JOJOCAFE/RV8/RV8GR/doc/labs/lab02_ring_counter.md

# Lab 02: Ring Counter — สร้างจังหวะ T0/T1/T2

**เป้าหมาย**: ต่อ U8 (74HC164) + U24 (74HC04) ให้สร้างจังหวะ 3 เฟส

---

## อุปกรณ์

| ชิ้น | ชื่อ | จำนวน |
|:----:|---|:-----:|
| 1 | 74HC164 (U8) | 1 |
| 2 | 74HC04 (U24) | 1 |
| 3 | LED สีเขียว 3mm | 3 |
| 4 | 330Ω resistor | 3 |
| 5 | 100nF capacitor | 2 |
| 6 | Push button (Reset) | 1 |
| 7 | 10kΩ resistor | 1 |

---

## วงจร

### Pinout: 74HC164 (U8)

```
        ┌───U───┐
   A  1 │       │ 14 VCC
   B  2 │       │ 13 Q7
  Q0  3 │ 164   │ 12 Q6
  Q1  4 │       │ 11 Q5
  Q2  5 │       │ 10 Q4
  Q3  6 │       │  9 /CLR
 GND  7 │       │  8 CLK
        └───────┘
```

### Pinout: 74HC04 (U24) — ใช้แค่ 2 gate

```
        ┌───U───┐
  1A  1 │       │ 14 VCC
  1Y  2 │       │ 13
  2A  3 │ 04    │ 12
  2Y  4 │       │ 11
     ...│       │...
 GND  7 │       │  8
        └───────┘
```

### การต่อสาย

```
1. ไฟเลี้ยง:
   U8 pin 14 (VCC) → 5V        U8 pin 7 (GND) → GND
   U24 pin 14 (VCC) → 5V       U24 pin 7 (GND) → GND
   100nF คร่อม VCC-GND ทั้ง 2 ตัว

2. Ring counter feedback:
   U8 pin 3 (Q0) → U24 pin 1 (1A)     [Q0 เข้า inverter 1]
   U24 pin 2 (1Y) → U8 pin 1 (A)      [NOT Q0 → A]
   
   U8 pin 4 (Q1) → U24 pin 3 (2A)     [Q1 เข้า inverter 2]
   U24 pin 4 (2Y) → U8 pin 2 (B)      [NOT Q1 → B]

3. Clock:
   U8 pin 8 (CLK) → สาย CLK จาก Lab 01 (ปุ่มกด)

4. Reset:
   U8 pin 9 (/CLR) → ปุ่ม Reset (ปกติ HIGH, กด = LOW)
   [ต่อ: 5V → 10kΩ → pin 9 ← ปุ่ม → GND]

5. LED ดู output:
   U8 pin 3 (Q0=T0) → 330Ω → LED → GND
   U8 pin 4 (Q1=T1) → 330Ω → LED → GND
   U8 pin 5 (Q2=T2) → 330Ω → LED → GND
```

---

## ทำไมวงจรนี้ถึงวนครบ 3?

74HC164: serial input = **A AND B** (ต้อง HIGH ทั้งคู่ถึงจะ shift 1 เข้า)

| สถานะ | Q2 Q1 Q0 | A=NOT(Q0) | B=NOT(Q1) | A AND B | ถัดไป |
|:---:|:---:|:---:|:---:|:---:|:-----:|
| Reset | 0 0 0 | 1 | 1 | **1** | 0 0 1 |
| T0 | 0 0 1 | 0 | 1 | **0** | 0 1 0 |
| T1 | 0 1 0 | 1 | 0 | **0** | 1 0 0 |
| T2 | 1 0 0 | 1 | 1 | **1** | 0 0 1 ← วนกลับ T0! |

วงจรนี้คือ **3-state FSM** — มี 3 สถานะ วนซ้ำ ตลอดไป

### Timing Diagram

```
CLK  ─┐ ┌─┐ ┌─┐ ┌─┐ ┌─┐ ┌─┐ ┌─┐ ┌─
      └─┘ └─┘ └─┘ └─┘ └─┘ └─┘ └─┘

T0   ───██████─────────────██████────
T1   ─────────██████─────────────████
T2   ─────────────────██████─────────

     │← 1 คำสั่ง →│← 1 คำสั่ง →│
```

### จังหวะนี้ใช้ทำอะไรใน CPU?

ทุกคำสั่งของ RV8-GR ใช้ 3 clock = 3 จังหวะ:

```
ตัวอย่าง: LI $42 (โหลดค่า $42 เข้า accumulator)

T0: อ่าน opcode $10 จาก ROM    → บอก CPU ว่า "LI"
T1: อ่าน operand $42 จาก ROM   → ค่าที่ต้องโหลด
T2: execute → AC ← $42          → ทำงานจริง!
```

LED 3 ดวงที่เห็นใน lab นี้ = สัญญาณจริงที่ไปควบคุม U5 (IR), U6 (IRL), U9 (AC), PC ทั้งหมดใน lab ถัดๆ ไป

> ⚠️ **เรื่อง Clock Bounce**
>
> Ring Counter เป็นจุดแรกที่ bounce สร้างปัญหาจริง
> ถ้ากดปุ่ม 1 ครั้งแล้ว LED กระโดดข้ามสถานะ (เช่น T0→T2 ข้าม T1)
> แสดงว่า bounce ทำให้เกิดหลาย clock edge
>
> วิธีแก้: กดปุ่มช้าๆ ค้างไว้สักครู่แล้วค่อยปล่อย
> ถ้ายังมีปัญหา → เพิ่ม capacitor 100nF ที่ปุ่มกด
> (lab ถัดไปจะเพิ่ม 74HC14 Schmitt Trigger ให้ clean ขึ้น)

---

## ทดสอบ ✅

### ขั้นตอน

1. เสียบไฟ → LED ทั้ง 3 อาจติดหรือดับ (ยังไม่ reset)
2. **กด Reset** → LED ทั้ง 3 ดับ (Q0=Q1=Q2=0)
3. **กด Clock ครั้งที่ 1** → T0 ติด, T1 ดับ, T2 ดับ
4. **กด Clock ครั้งที่ 2** → T0 ดับ, T1 ติด, T2 ดับ
5. **กด Clock ครั้งที่ 3** → T0 ดับ, T1 ดับ, T2 ติด
6. **กด Clock ครั้งที่ 4** → T0 ติด! (วนกลับมา!)

### ตาราง LED

| กด Clock | T0 (Q0) | T1 (Q1) | T2 (Q2) | ถูก? |
|:---:|:---:|:---:|:---:|:----:|
| Reset | ○ | ○ | ○ | ☐ |
| 1 | ● | ○ | ○ | ☐ |
| 2 | ○ | ● | ○ | ☐ |
| 3 | ○ | ○ | ● | ☐ |
| 4 | ● | ○ | ○ | ☐ |
| 5 | ○ | ● | ○ | ☐ |
| 6 | ○ | ○ | ● | ☐ |

● = LED ติด, ○ = LED ดับ

### ทดสอบความทนทาน

| # | ทดสอบ | ผลที่ต้องได้ | ผ่าน? |
|:-:|---|---|:-----:|
| 6 | ต่อ 555 timer (1Hz) ปล่อย 1000+ cycles | T0→T1→T2 ไม่เคยหลุด | ☐ |

> 📌 **Illegal State Recovery**: หาก power-up ได้สถานะผิด
> วงจรจะเข้าสู่ลูป T0→T1→T2 ได้เองภายในไม่กี่ clock cycles
> (feedback A AND B = NOT(Q0) AND NOT(Q1) ทำหน้าที่ self-correct)
> ถ้ารอ 5-6 clocks แล้วยังไม่วนปกติ → กด Reset ให้ Q0-Q2=000
> แล้วปล่อย clock 1 ครั้งเพื่อเข้า T0

### State Machine (ภาพรวมหัวใจ CPU)

```
        ┌────────────────────────────┐
        │                            │
        ▼                            │
    ┌───────┐     ┌───────┐     ┌───────┐
    │  T0   │────→│  T1   │────→│  T2   │
    │ (001) │     │ (010) │     │ (100) │
    │ Fetch │     │Operand│     │Execute│
    └───────┘     └───────┘     └───────┘
```

> ทุกคำสั่งใน RV8-GR วนรอบนี้ตลอด — ไม่มี stall, ไม่มี wait state

### Optional: Debug Header (Q3-Q7)

ถ้าอยากตรวจ illegal state ได้ชัดขึ้น:

```
U8 pin 6  (Q3) → test point (หรือ LED)
U8 pin 10 (Q4) → test point
U8 pin 11 (Q5) → test point
U8 pin 12 (Q6) → test point
U8 pin 13 (Q7) → test point
```

> ปกติ Q3-Q7 ต้องเป็น 0 ตลอด
> ถ้าเห็น Q3+ ติด = ring counter หลุด state → กด Reset

---

## ถ้าไม่ถูก?

| อาการ | สาเหตุ | แก้ |
|---|---|-----|
| LED ไม่ติดเลย | ไฟไม่ถึง IC | เช็ค VCC/GND |
| T0 ค้างติดตลอด | inverter ต่อผิด | เช็ค U24 pin 1→2, pin 3→4 |
| วนไม่ครบ 3 | A,B ต่อสลับ | สลับ U8 pin 1 กับ pin 2 |
| กด Reset แล้วไม่ clear | /CLR ไม่ถึง LOW | เช็คปุ่ม Reset |

---

## ซอฟต์แวร์จำลอง

รัน sim_lab เปรียบเทียบ:
```bash
cd RV8GR/sim/sim_lab
python3 lab02_ring_counter.py
```

---

## สิ่งที่ได้

- ✅ จังหวะ T0→T1→T2 วนได้ถูกต้อง
- ✅ CPU ต้องการจังหวะนี้เพื่อทำงาน 3 ขั้นตอน/คำสั่ง
- ✅ T0 = อ่านคำสั่ง, T1 = อ่าน operand, T2 = ทำงาน

### สิ่งที่พิสูจน์ได้แล้ว

```
✓ มี clock (Lab 01)
✓ มี reset (Lab 01)
✓ มี state machine (Lab 02) ← อยู่ตรงนี้!
✓ มี one-hot encoding
✓ มี fetch/execute timing
```

> 📌 CPU ที่เหลือทั้งหมด (U1-U34) จะใช้ T0/T1/T2 นี้เป็นจังหวะกลางร่วมกัน
> LED 3 ดวงนี้ = สัญญาณจริงที่ควบคุม CPU ทั้งตัว!

**ผ่านทุกข้อ → ไป Lab 03!** 🎉
