JOJOCAFE/RV8/JOJOCAFE-Org/.agent_state/sw-coder/MEMORY.md

# SW Coder Memory

## Tools Built

| Tool | Status | Purpose |
|---|---|---|
| `tools/rv8gr_asm.py` | ✅ done | Assembler (18 opcodes + macros) |
| `sim/chip_sim.py` | ✅ done | Gate-level sim (34 logic chips + ROM/RAM) |
| `sim/soft_debug.py` | ✅ done | High-level trace sim |
| `rv8flash.py` | ✅ done | ROM programmer (flash/read/verify) |
| `rv8term.py` | ✅ done | Terminal bridge via /SLOT1 |

## Assembler Features

- 18 opcodes + macros (CLR, INC, DEC, NOT, NOTI)
- Cross-page validation
- Overlap detection
- .memh output for Verilog
- Page-safe branch checking

## ISA Quick Ref

- Immediate: opcode, imm (2 bytes, SRC=0)
- Register: opcode, rs/rd (2 bytes, SRC=1 or STR=1)
- Branch/Jump: opcode, addr_lo (2 bytes, uses Page Register)

## Programmer Protocol

- `?` → `Connected\n` (identify)
- `F` + 32KB → `D\n` (flash)
- `V` → 32KB (verify/read)
- `R` → `K\n` (run mode)

## Pending

- Example programs (.asm): blink, counter, game, BASIC stub
- RV8-R assembler (when ISA designed)
- Components backend now has schematic/netlist/probe/test-logic foundations. Next work should keep JSON/block/Python APIs round-trippable and frontend-agnostic.

## Components Python Simulator

- Shared path: `/home/jo/kiro/Components/python`
- `chiplib.loader` loads `.bin`, Intel HEX, or text-hex into ROM/RAM `.data` before simulation.
- `StimulusController` default is 64 input channels (`IN0..IN63`) and 8 clock channels (`CLK0..CLK7`).
- Keep the backend frontend-agnostic for future JS/web service wrappers or Python-native UI.
- Clock stimulus is edge-aware and should drive physical pins, not abstract CPU clocks.
