JOJOCAFE/RV8/RV8GR/doc/labs/lab03_pc_counter.md

# Lab 03: Program Counter — นับตำแหน่งคำสั่ง

**เป้าหมาย**: ต่อ U1-U4 (74HC161 ×4) เป็น counter 16 บิต นับขึ้นทีละ 1

---

## อุปกรณ์

| ชิ้น | ชื่อ | จำนวน |
|:----:|---|:-----:|
| 1 | 74HC161 (U1-U4) | 4 |
| 2 | LED สีเขียว 3mm | 8 |
| 3 | 330Ω resistor | 8 |
| 4 | 100nF capacitor | 4 |

---

## วงจร

### Pinout: 74HC161

```
          ┌───U───┐
  /CLR  1 │       │ 16 VCC
   CLK  2 │       │ 15 RCO
    D0  3 │ 161   │ 14 QA (bit 0)
    D1  4 │       │ 13 QB (bit 1)
    D2  5 │       │ 12 QC (bit 2)
    D3  6 │       │ 11 QD (bit 3)
   ENP  7 │       │ 10 ENT
   GND  8 │       │  9 /LD
          └───────┘
```

### การต่อสาย

```
ทุกตัว (U1-U4):
  pin 16 (VCC) → 5V
  pin 8 (GND) → GND
  pin 1 (/CLR) → ปุ่ม Reset (ปกติ HIGH)
  pin 2 (CLK) → สาย CLK จาก Lab 01
  pin 7 (ENP) → 5V (enable นับตลอด)
  pin 9 (/LD) → 5V (ไม่ load, นับอย่างเดียว)
  100nF คร่อม VCC-GND ทุกตัว

Cascade (ต่อพ่วง):
  U1 pin 10 (ENT) → 5V (ตัวแรก enable ตลอด)
  U1 pin 15 (RCO) → U2 pin 10 (ENT)
  U2 pin 15 (RCO) → U3 pin 10 (ENT)
  U3 pin 15 (RCO) → U4 pin 10 (ENT)

LED (ดู 8 บิตล่าง = U1 + U2):
  U1 pin 14 (QA=bit0) → 330Ω → LED → GND
  U1 pin 13 (QB=bit1) → 330Ω → LED → GND
  U1 pin 12 (QC=bit2) → 330Ω → LED → GND
  U1 pin 11 (QD=bit3) → 330Ω → LED → GND
  U2 pin 14 (QA=bit4) → 330Ω → LED → GND
  U2 pin 13 (QB=bit5) → 330Ω → LED → GND
  U2 pin 12 (QC=bit6) → 330Ω → LED → GND
  U2 pin 11 (QD=bit7) → 330Ω → LED → GND
```

---

## ทดสอบ ✅

### ขั้นตอน

1. กด Reset → LED ทั้ง 8 ดับ (PC = 0000 0000)
2. กด Clock ทีละครั้ง → LED นับขึ้น:

### ตาราง LED (อ่านจากขวาไปซ้าย = bit7...bit0)

| กด | bit7 | bit6 | bit5 | bit4 | bit3 | bit2 | bit1 | bit0 | ค่า | ถูก? |
|:--:|:----:|:----:|:----:|:----:|:----:|:----:|:----:|:----:|:---:|:----:|
| Reset | ○ | ○ | ○ | ○ | ○ | ○ | ○ | ○ | $00 | ☐ |
| 1 | ○ | ○ | ○ | ○ | ○ | ○ | ○ | ● | $01 | ☐ |
| 2 | ○ | ○ | ○ | ○ | ○ | ○ | ● | ○ | $02 | ☐ |
| 3 | ○ | ○ | ○ | ○ | ○ | ○ | ● | ● | $03 | ☐ |
| 4 | ○ | ○ | ○ | ○ | ○ | ● | ○ | ○ | $04 | ☐ |
| 15 | ○ | ○ | ○ | ○ | ● | ● | ● | ● | $0F | ☐ |
| 16 | ○ | ○ | ○ | ● | ○ | ○ | ○ | ○ | $10 | ☐ |

● = LED ติด (1), ○ = LED ดับ (0)

**สำคัญ**: ถ้ากด 16 ครั้งแล้ว bit4 ติด = cascade ทำงาน!

> 📝 **หมายเหตุ: PC จริงใน RV8-GR**
>
> Lab นี้ต่อ ENP=ENT=VCC ทำให้ PC นับ **ทุก clock** เพื่อความง่าย
>
> แต่ใน CPU จริง PC จะนับเฉพาะ T0 และ T1 (ไม่นับใน T2)
> ผ่านสัญญาณ `PC_INC = T0 OR T1` จาก Ring Counter (Lab 02)
>
> ```
> U4  U3  U2  U1
> [15:12] [11:8] [7:4] [3:0]  ← PC 16 บิตเต็ม
> ```
>
> LED 8 ดวงที่เห็นใน lab นี้ = PC[7:0] เท่านั้น (PC[15:8] ยังมีอยู่ใน U3-U4)

---

## ถ้าไม่ถูก?

| อาการ | สาเหตุ | แก้ |
|---|---|-----|
| ไม่นับเลย | ENP หรือ ENT ไม่ HIGH | เช็คสาย pin 7, 10 |
| นับแค่ 0-15 วน | U2 ENT ไม่ต่อ U1 RCO | ต่อ U1-15 → U2-10 |
| นับ 2 ทีละครั้ง | Clock bounce | เพิ่ม 100nF ที่ปุ่ม |
| Reset ไม่ทำงาน | /CLR ค้าง HIGH | เช็คปุ่ม Reset |

---

## ซอฟต์แวร์จำลอง

```bash
cd RV8GR/sim/sim_lab
python3 lab03_pc_counter.py
```

---

## Challenge (ไม่บังคับ — สำหรับคนที่อยากลองเพิ่ม)

### Challenge A: PC_INC — ให้ Ring Counter ควบคุม PC

```
ถอด ENP/ENT จาก VCC
ต่อ ENP (U1-7) ← T0 (U8-3) [หรือ T0 OR T1]
ต่อ ENT (U1-10) ← T0 (U8-3)
```

สังเกต: PC จะนับเฉพาะเมื่อ T0=HIGH → **Control Unit ควบคุม PC!**

### Challenge B: Parallel Load — ทำ Jump

```
ต่อ DIP switch 4 บิต → U1 pin 3,4,5,6 (D0-D3)
ดึง /LD (pin 9) ลง LOW (ปุ่มกด)
กด Clock → PC โหลดค่าจาก switch!
```

นี่คือวิธีที่คำสั่ง J (Jump) ทำงานใน CPU จริง:
/PC_LD = LOW → PC ← target address

---

## สิ่งที่ได้

- ✅ Counter 16 บิต นับ $0000 → $FFFF
- ✅ Reset กลับ $0000 ได้
- ✅ Cascade: U1 เต็ม → U2 นับต่อ → U3 → U4
- ✅ นี่คือ Program Counter ของ CPU!

**ผ่านทุกข้อ → ไป Lab 04!** 🎉
