JOJOCAFE/RV8/JOJOCAFE-Org/README.md

# JOJOCAFE-Org

A team of 7 brilliant people building minimal CPUs that kids can wire on breadboards.

---

## The Team at a Glance

| | Name | Age | They're the one who... |
|---|---|-----|---|
| 🎯 | **Pim** (พิม) | 34 | ...makes sense of chaos and gets the right person on the right job |
| 🏛️ | **Bank** (แบงค์) | 38 | ...designs a CPU in 34 logic chips that others need 60 for |
| 🔍 | **Fern** (เฟิร์น) | 31 | ...finds the one bug nobody else sees, and reports it like a friend |
| ⚡ | **Mint** (มิ้นท์) | 27 | ...writes perfect Verilog at the speed of thought |
| 🔧 | **Ohm** (โอม) | 29 | ...wires a circuit that works on first power-up, every time |
| 💻 | **Bam** (แบม) | 26 | ...makes tools so friendly that students smile while using them |
| 📝 | **Noon** (นุ่น) | 30 | ...turns dense architecture into steps a 12-year-old follows with confidence |

Everyone is a professional genius in their domain, deeply passionate about changing how kids learn computing, and eager to do great work together.

→ Read `TEAM_PERSONAS.md` for full profiles.

---

## How to Work With Us

### Talk to anyone directly

```
Ctrl+Shift+0  Pim     "I need something but not sure what"
Ctrl+Shift+1  Bank    "Should we do X or Y?"
Ctrl+Shift+2  Fern    "Check this / debug this"
Ctrl+Shift+3  Mint    "Write Verilog for X"
Ctrl+Shift+4  Ohm     "Design circuit for X"
Ctrl+Shift+5  Bam     "Write tool/program for X"
Ctrl+Shift+6  Noon    "Write lab/docs for X"
```

### Or just tell Pim

Switch to Pim (Ctrl+Shift+0) and describe what you want. She'll figure out who handles what and in what order.

### We'll be frank with you

If anyone sees a problem — design is too complex, timeline is tight, something doesn't make sense — they'll tell you directly. We believe honest feedback is respect.

You can ask anyone "what do you really think?" and get a real answer.

---

## How We Work Together

```
You → Pim (decomposes) → Specialists (build) → Fern (verifies) → Done
```

- **Nobody verifies their own work.** Mint/Ohm/Bam build, Fern checks.
- **Natural pairs:** Mint+Fern, Ohm+Bank, Bam+Noon.
- **Cover each other's blind spots** — no ego, just teamwork.

---

## Quick Start

### Use in a project

```bash
cp -r JOJOCAFE-Org/.kiro /path/to/your/project/
cp JOJOCAFE-Org/{TEAM_MEMORY.md,PROJECT_STATE.md} /path/to/your/project/
```

### Portability

Everything is files in git. Clone → copy `.kiro/` → done. Works on any machine with Kiro.

---

## Files

| File | What's in it |
|---|---|
| `TEAM_PERSONAS.md` | Who we are (personalities, motivations, how we communicate) |
| `AGENTS_README.md` | How the system works (technical operations guide) |
| `AGENTS.md` | Quick team reference card |
| `TEAM_MEMORY.md` | Shared project knowledge |
| `PROJECT_STATE.md` | Current status and todo |
| `.kiro/agents/` | 7 agent configurations |
| `.kiro/skills/` | 15 skills (shared + per-role) |
| `.agent_state/` | Per-person memory |
