JOJOCAFE/RV8/RV8GR/doc/05_understand_by_module.md

# RV8-GR — เข้าใจ CPU ทีละโมดูล (สำหรับน้อง ม.ต้น)

**สอน CPU 34 logic chips + ROM + RAM ตัวนี้ทีละขั้น ใช้ภาษาง่ายๆ ไม่รีบ อ่านจบแล้วต่อวงจรได้เลย**

---

## สารบัญ

1. CPU คืออะไร — ภาพรวม
2. จังหวะนาฬิกา T0/T1/T2 (U8)
3. Program Counter — ตัวชี้คำสั่ง (U1-U4)
4. Instruction Register — ตัวจำคำสั่ง (U5, U6)
5. DBUS, IBUS — ถนนข้อมูล (U7, U14)
6. ALU — เครื่องคำนวณ (U10-U13, U19-U20)
7. AC Mux — เลือกผลลัพธ์ (U17-U18)
8. Address Mux — เลือกที่อยู่ (U15-U16, U29-U30)
9. Z Flag — ธงศูนย์ (U21, U22)
10. Page Register — กระโดดไกล (U23)
11. Control Logic — สมองสั่งการ (U24-U28)
12. IRQ — ขัดจังหวะ (U31)
13. ROM กับ RAM — หน่วยความจำ
14. RV8-Bus — ถนนสู่โลกภายนอก (40-pin)
15. สรุป: ข้อมูลไหลอย่างไร
16. คำสั่งทั้งหมดของ RV8-GR (ISA)
17. CPU ทำงานจริง — ไล่ทีละ Clock
18. อ่านจบแล้ว ทำอะไรต่อ?

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

---

## 1. CPU คืออะไร — ภาพรวม

CPU เหมือนสมองของคอมพิวเตอร์ มันทำ 3 สิ่ง ซ้ำไปเรื่อยๆ:

### ภาพรวมทั้ง CPU (จำภาพนี้ไว้ตลอดทั้งเล่ม!)

```
                    ┌─────────┐
        ┌──────────│   ROM   │ ← เก็บโปรแกรม
        │          └─────────┘
        │               ↕ DBUS (ถนนภายนอก)
        │          ┌─────────┐
        │          │   U7    │ ← สะพานเชื่อม
        │          └─────────┘
        │               ↕ IBUS (ถนนภายใน)
        │    ┌──────────┼──────────┐
        │    │          │          │
   ┌────┴──┐│    ┌─────┴────┐   ┌─┴───┐
   │  PC   ││    │   ALU    │   │ AC  │ ← ผลลัพธ์
   │(U1-U4)││    │(U10-U13) │   │(U9) │
   └───────┘│    └──────────┘   └─────┘
        ↑   │          ↑              │
        │   │    ┌─────┴────┐         │
   กระโดด  │    │  IR (U5) │ ← คำสั่ง │
        │   │    └──────────┘         ↓
        │   │                    ┌─────────┐
        │   └───────────────────→│   RAM   │ ← เก็บข้อมูล
        │                        └─────────┘
   Page Reg (U23)
```

### Fetch → Fetch → Execute (หัวใจของ CPU!)

CPU ตัวนี้ไม่มี "Decode" แยก เพราะ opcode = สัญญาณควบคุมโดยตรง!

ทุกคำสั่งใช้ 3 จังหวะ ลองดูตัวอย่าง `ADDI $05` (บวก 5):

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

```
T0: PC ชี้ ROM → ได้ "$10" → IR จำไว้ (="บวก")
T1: PC ชี้ ROM → ได้ "$05" → IR จำไว้ (="5")
T2: ALU ทำ AC + 5 → AC = ผลลัพธ์ใหม่!
```

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

```
1. อ่านคำสั่ง (จาก ROM)
2. เข้าใจคำสั่ง (แปลเป็นสัญญาณ)
3. ทำตามคำสั่ง (คำนวณ, เก็บค่า, กระโดด)
```

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

ทั้งหมดนี้ทำได้ด้วย 34 logic chips ไม่มี microcode ไม่มี lookup table.

---

## 2. จังหวะนาฬิกา T0/T1/T2 (U8)

**ทำไมต้องมีจังหวะ?**

ลองนึกภาพการทำขนมปัง:
1. หยิบแป้ง (T0)
2. ใส่ไส้ (T1)
3. ปิ้ง (T2)

CPU ก็เหมือนกัน — ทำทีละขั้น ขั้นละ 1 จังหวะนาฬิกา.

**ชิป U8 (74HC164)** สร้างจังหวะ:

```
CLK:  ⎽⎽⎽⎽╱‾‾‾‾╲⎽⎽⎽⎽╱‾‾‾‾╲⎽⎽⎽⎽╱‾‾‾‾╲⎽⎽⎽⎽╱‾‾‾‾╲⎽⎽⎽

T0:   ‾‾‾‾‾‾‾‾‾‾╲⎽⎽⎽⎽⎽⎽⎽⎽⎽⎽⎽⎽⎽⎽⎽⎽⎽⎽⎽⎽⎽⎽⎽╱‾‾‾‾‾‾‾‾‾‾
T1:   ⎽⎽⎽⎽⎽⎽⎽⎽⎽⎽╱‾‾‾‾‾‾‾‾‾‾╲⎽⎽⎽⎽⎽⎽⎽⎽⎽⎽⎽⎽⎽⎽⎽⎽⎽⎽⎽⎽⎽⎽⎽
T2:   ⎽⎽⎽⎽⎽⎽⎽⎽⎽⎽⎽⎽⎽⎽⎽⎽⎽⎽⎽⎽⎽╱‾‾‾‾‾‾‾‾‾‾╲⎽⎽⎽⎽⎽⎽⎽⎽⎽⎽⎽
        T0          T1          T2          T0 ...
```

มีบิตเดียวที่เป็น 1 วิ่งไป: Q0→Q1→Q2→Q0...

```
State Diagram (หัวใจ CPU):

    RESET → [T0] → [T1] → [T2] ─┐
              ↑                    │
              └────────────────────┘

ภายใน Shift Register:

    [1][0][0]  ← T0 active
         ↓ clock
    [0][1][0]  ← T1 active
         ↓ clock
    [0][0][1]  ← T2 active
         ↓ clock (feedback วนกลับ)
    [1][0][0]  ← T0 อีกรอบ!
```

> 📌 มีบิต "1" เพียงตัวเดียววิ่งวนในวงแหวน — เรียกว่า **one-hot encoding**
> ถ้ารีเซ็ต จะกลับมาเป็น T0 เสมอ

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

---

## 3. Program Counter — ตัวชี้คำสั่ง (U1-U4)

**ทำไมต้องมี PC?**

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

**ชิป**: U1-U4 (74HC161 × 4 ตัว = 16 บิต)

```
ทำงาน 3 แบบ:
1. นับขึ้น +1  (ตอน T0, T1 → อ่านคำสั่งถัดไป)
2. หยุดนับ     (ตอน T2 → ทำงาน ไม่ต้องอ่านเพิ่ม)
3. กระโดด     (ตอน jump → ใส่ค่าใหม่เข้า PC)
```

**ตัวอย่าง**:
```
PC = $0000 → อ่าน ROM ที่ $0000 (คำสั่ง LI $10)
PC = $0001 → อ่าน ROM ที่ $0001 (operand $10)
PC = $0002 → อ่าน ROM ที่ $0002 (คำสั่งถัดไป)
...
PC = $0020 ← J $20 สั่ง jump → PC กระโดดไปตรงนี้!
```

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

---

## 4. Instruction Register — ตัวจำคำสั่ง (U5, U6)

**ทำไมต้องจำคำสั่ง?**

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

ต้องจำไว้เพื่อใช้ตอน T2 (execute).

**U5 (IR_HIGH)** — จำ control byte:
```
ตัวอย่าง: ADDI → control byte = $10 = 00010000
                                        │││││││└─ JMP=0
                                        ││││││└── BR=0
                                        │││││└─── STR=0
                                        ││││└──── SRC=0
                                        │││└───── AC_WR=1 ← เขียน AC!
                                        ││└────── MUX_SEL=0
                                        │└─────── XOR_MODE=0
                                        └──────── ALU_SUB=0
```

**U6 (IR_LOW)** — จำ operand:
```
ตัวอย่าง: ADDI $05 → operand = $05 = ค่าที่จะบวก
```

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

---

## 5. DBUS, IBUS — ถนนข้อมูล (U7, U14)

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

**2 ถนนข้อมูล:**

```
┌─────────────────────────────────────────────────┐
│  โลกภายนอก (ROM, RAM)                            │
│          ↕ DBUS (D0-D7)                          │
│      ┌───────┐                                   │
│      │  U7   │  ← Bus Buffer (สะพาน)             │
│      └───────┘                                   │
│          ↕ IBUS (IBUS0-IBUS7)                        │
│  โลกภายใน (ALU, registers)                       │
└─────────────────────────────────────────────────┘
```

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

**กฎสำคัญ: ทางเดินเดียว!**

IBUS มี 3 คนที่ส่งข้อมูลได้ แต่ **ทีละคนเท่านั้น**:

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

```
U7 /OE = BUF_OE_N
WR_DIR = NOT(/AC_BUF)
ROM /OE = WR_DIR
→ ถ้า STR=1 (STORE active): U14 ขับ IBUS, U7 ส่ง IBUS→DBUS, ROM ปิด output
```

---

## 6. ALU — เครื่องคำนวณ (U10-U13, U19-U20)

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

**เคล็ดลับ: ใช้ XOR gate ทำทั้ง 3 อย่าง!**

```
                    IBUS (ค่าที่จะคำนวณ)
                      │
              ┌───────┴───────┐
              │   U12-U13     │  ← XOR gates
              │   A=IBUS      │
              │   B=??? ←─────┼── U19-U20 (mux เลือก)
              └───────┬───────┘
                      │
              XOR output
                ╱          ╲
    ┌──────────┘            └──────────┐
    │ U10-U11 (Adder)                  │ U17-U18 (AC mux B)
    │ A = AC                           │ → ส่งตรงเข้า AC
    │ B = XOR output                   │   (สำหรับ LI, XOR)
    │ Cin = SUB bit                    │
    │ SUM = ผลบวก                      │
    └──────────────────────────────────┘
```

**3 โหมด:**

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

**ทำไมลบได้?**
```
ลบ = บวกกับจำนวนลบ
จำนวนลบ = กลับบิต + 1 (two's complement)
กลับบิต = XOR กับ 1111 1111
+1 = Cin=1 (ใส่ carry เข้า adder)
```

**ตัวอย่าง: 5 - 3 ทีละขั้น:**
```
5 = 00000101

ขั้น 1: เอา 3 มากลับบิต
  3 = 00000011
  กลับ = 11111100

ขั้น 2: +1
  11111100 + 1 = 11111101  ← นี่คือ "-3"!

ขั้น 3: บวก 5 + (-3)
  00000101
+ 11111101
-----------
  00000010  = 2 ✓ (5-3=2!)
```

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

---

## 7. AC Mux — เลือกผลลัพธ์ (U17-U18)

**ทำไมต้องเลือก?**

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

Mux เลือกว่าจะส่งอันไหนเข้า AC:

```
MUX_SEL=0: Adder SUM → AC     (ADD, SUB, ADDI, SUBI)
MUX_SEL=1: XOR output → AC    (LI, LB, XORI, XOR)
```

**เคล็ดลับ LI (Load Immediate):**
```
LI $42: ต้องการ AC = $42
- IBUS = $42 (จาก IRL)
- XOR B = 0 (XOR_MODE=0, ALU_SUB=0)
- XOR output = $42 XOR 0 = $42 (ผ่านตรง!)
- MUX_SEL=1 → AC = XOR output = $42
```

ไม่ต้องมีสายตรงจาก IBUS เข้า AC — ประหยัดชิป!

---

## 8. Address Mux — เลือกที่อยู่ (U15-U16, U29-U30)

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

**Mux เลือก:**

```
/ADDR_MODE=1 (T0, T1): A[15:0] = PC          → อ่าน ROM/RAM ตาม PC
/ADDR_MODE=0 (data T2): A[7:0]  = IRL         → low byte จาก operand
                       A[15:8] = Data Page   → high byte จาก U32
```

**Data Page Register (U32):**
```
SETDP $90     → Data Page = $90
LB $05        → อ่าน RAM[$9005] (ไม่ใช่ $0005!)
SB $20        → เขียน RAM[$9020]

SETDP $00     → Data Page = $00
LB $00        → อ่าน ROM[$0000] (lookup table!)

SETDP $80     → กลับมาที่ registers ($8000-$80FF)
```

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

**Chip Select จาก A15:**
```
A15=0 → ROM ทำงาน (address $0000+) — อ่านได้อย่างเดียว
A15=1 → RAM ทำงาน (address $8000+) — อ่านและเขียนได้
```

---

## 9. Z Flag — ธงศูนย์ (U21, U22)

**ทำไมต้องมี Z flag?**

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

**วิธีทำงาน:**

```
U22 (74HC688): เปรียบเทียบ AC กับ $00
  → ถ้า AC = $00: ส่งสัญญาณ LOW

U21 (74HC74): เก็บผลลัพธ์
  → U22 LOW → preset Z = 1 (ใช่! AC เป็นศูนย์)
  → U22 HIGH → Z = 0 (ไม่ใช่)
```

> 📌 Z อัปเดต**ทันที**หลัง AC เปลี่ยนค่า (async preset — ไม่ต้องรอ clock)
> แต่ BEQ/BNE จะ**ดูค่า Z ตอน T2** เท่านั้น — ไม่ใช่ระหว่าง T0/T1

**ตัวอย่าง:**
```
LI $05    → AC=$05 → Z=0 (ไม่ใช่ศูนย์)
SUBI $05  → AC=$00 → Z=1 (เป็นศูนย์!)
BEQ $20   → Z=1 → กระโดดไป $20!
```

---

## 10. Page Register — กระโดดไกล (U23)

**ปัญหา**: Operand มีแค่ 8 บิต → jump ได้แค่ 256 ตำแหน่ง!

**วิธีแก้**: ใช้ Page Register เป็น high byte:

```
SETPG $90     → Page Register = $90
J $00         → PC = {$90, $00} = $9000
```

ตอน jump: PC ใหม่ = {Page Register, Operand} = 16 บิต → jump ได้ทั้ง 64KB!

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

> 📌 **อย่าสับสน! มี Register 2 ตัวที่คล้ายกัน:**
>
> | Register | ชิป | ใช้กับ | ตั้งค่าด้วย |
> |----------|-----|--------|-------------|
> | Page Register (PG) | U23 | **Jump** — กำหนด PC[15:8] | SETPG |
> | Data Page (DP) | U32 | **Load/Store** — กำหนด address[15:8] | SETDP |
>
> ```
> Jump:   PC = {PG, operand}      ← SETPG กำหนด
> Data:   addr = {DP, operand}    ← SETDP กำหนด
> ```

---

## 11. Control Logic — สมองสั่งการ (U24-U28)

**ชิปเหล่านี้ทำอะไร?**

สร้าง control signals ที่ซับซ้อนจากสัญญาณง่ายๆ:

```
U24 (Inverters): กลับสัญญาณ
  - NOT(T0), NOT(T1) → feedback ให้ ring counter
  - NOT(A15) → RAM /CE (RAM active when A15=1)
  - NOT(JUMP), NOT(AC_WR) → ใช้ในเงื่อนไข

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

U28 (XOR gates): สัญญาณพิเศษ
  - Z_match: ใช้ SUB bit กลับเงื่อนไข (BEQ vs BNE)
  - /T2: ใช้กับ Page Register timing
  - WR_DIR: ทิศของ U7 bus buffer
```

---

## 12. IRQ — ขัดจังหวะ (U31)

**IRQ คืออะไร?**

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

**v1.0: Polling Model (ไม่มี hardware vector)**
```
1. ขา /IRQ ถูกดึง LOW แล้วปล่อยกลับ HIGH → rising edge ทำให้ IRQ_FF = 1
2. Main loop ตรวจ IRQ_FF ถ้ามีอุปกรณ์ /SLOT ภายนอก expose latch นี้ให้ software อ่าน
3. ถ้า IRQ_FF=1 AND IE=1:
   - Software branch ไป handler
   - จัดการ event ตาม software policy
   - อย่าเรียก EI ซ้ำ เว้นแต่ software ต้องการให้ IE=1
```

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

**คำสั่ง:**
```
EI ($08): เปิดรับ interrupt
DI ($48): ไม่มีผลกับ hardware v1.0
```

---

## 13. ROM กับ RAM — หน่วยความจำ

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

### ทำไม Register อยู่ใน RAM?

CPU ปกติ (เช่น Z80) มี register อยู่ในชิป CPU เลย:
```
A, B, C, D, E, H, L ← อยู่ข้างใน CPU
```

แต่ RV8-GR ประหยัดชิป → เก็บ register ไว้ใน RAM แทน:
```
$8000 = R0 (general purpose)
$8001 = R1
$8002 = R2
...
$8007 = R7
```

**ตัวอย่าง: R2 = R0 + R1**
```asm
LB $00      ; AC = R0 (อ่าน RAM[$8000])
ADD $01     ; AC = AC + R1 (บวกกับ RAM[$8001])
SB $02      ; R2 = AC (เขียนลง RAM[$8002])
```

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

**Memory Map ทั้งหมด:**
```
$0000-$7FFF  ROM (โปรแกรม, อ่านอย่างเดียว)
$8000-$FEFF  RAM (ข้อมูล, อ่าน+เขียน)
$FF00-$FF0F  RAM (available; future vector)
$FF10-$FF1F  I/O Slot 1 ← ไม่ใช่ RAM! เป็นช่องต่ออุปกรณ์
$FF20-$FF2F  I/O Slot 2 ← ไม่ใช่ RAM! เป็นช่องต่ออุปกรณ์
$FF30-$FFFF  RAM (เหลือใช้)
```

> 📌 $FF10-$FF2F ดูเหมือน RAM address แต่จริงๆ ต่อไปที่อุปกรณ์ภายนอก (Memory-Mapped I/O)

**Chip Select:**
```
A15 = 0 → ROM active  (address $0000+)
A15 = 1 → RAM active  (address $8000+)
```

สายเส้นเดียว A15 ตัดสินทุกอย่าง!

---

## 14. RV8-Bus — ถนนสู่โลกภายนอก (40-pin)

**ทำไมต้องมี Bus?**

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

RV8-Bus คือ **สายเชื่อม 40 เส้น** ที่ส่งทุกสัญญาณที่จำเป็นออกมา:

```
┌────────────────────────────────────────────┐
│          CPU Board (36 packages)              │
│                                            │
│  ┌──────────────────────────────────────┐  │
│  │     RV8-Bus (40-pin IDC socket)      │  │
│  └──┬───┬───┬───┬───┬───┬───┬───┬───┬──┘  │
└─────┼───┼───┼───┼───┼───┼───┼───┼───┼─────┘
      │   │   │   │   │   │   │   │   │
   A[15:0] D[7:0] CLK /WR /RD /IRQ /SLOT VCC GND
      │   │   │   │   │   │   │   │   │
┌─────┼───┼───┼───┼───┼───┼───┼───┼───┼─────┐
│  ┌──┴───┴───┴───┴───┴───┴───┴───┴───┴──┐  │
│  │     RV8-Bus (40-pin IDC plug)        │  │
│  └──────────────────────────────────────┘  │
│          Peripheral Board                  │
│  (Programmer, UART, LCD, Keyboard...)      │
└────────────────────────────────────────────┘
```

**สัญญาณสำคัญ:**

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

**I/O Slot Address:**
```
$FF10-$FF1F → /SLOT1 active (เช่น UART)
$FF20-$FF2F → /SLOT2 active (เช่น LCD)
```

CPU เขียน SB $00 ที่ page $FF → ข้อมูลไปถึง peripheral ผ่าน bus!

---

## 15. สรุป: ข้อมูลไหลอย่างไร

### ตัวอย่าง: ADDI $05 (AC = AC + 5)

```
┌─ T0: อ่านคำสั่ง ──────────────────────────────────────────┐
│  PC($0000) → Addr Mux → ABUS → ROM → DBUS → U7 → IBUS    │
│  → U5 latch control byte ($10)                             │
│  PC นับขึ้น → $0001                                         │
└─────────────────────────────────────────────────────────────┘

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

┌─ T2: ทำงาน! ───────────────────────────────────────────────┐
│  U34 → IBUS ($05)                                           │
│  → U12 XOR (ผ่านตรง เพราะ ALU_SUB=0)                           │
│  → U10 Adder: AC($10) + $05 = $15                         │
│  → U17 Mux (เลือก Adder)                                   │
│  → U9 AC latch = $15 ✓                                     │
└─────────────────────────────────────────────────────────────┘
```

### ตัวอย่าง: SB $03 (RAM[$8003] = AC)

```
┌─ T2: เขียน RAM ────────────────────────────────────────────┐
│  Address: U6($03) → Addr Mux → ABUS = $8003                │
│  Data: U9(AC) → U14 buf → IBUS → U7(DIR=write) → DBUS     │
│  RAM /CE=0 (A15=1), RAM /WE=0 → เขียนค่า!                   │
└─────────────────────────────────────────────────────────────┘
```

### ตัวอย่าง: J $20 (กระโดดไป $0020)

```
┌─ T2: กระโดด ───────────────────────────────────────────────┐
│  JMP=1 → PC_LOAD_COND=1 → /PC_LD=0                        │
│  PC load: D[7:0] = IRL = $20                               │
│           D[15:8] = Page Reg = $00                          │
│  → PC = $0020 ✓                                            │
└─────────────────────────────────────────────────────────────┘
```

---

## 16. คำสั่งทั้งหมดของ RV8-GR (ISA)

CPU ตัวนี้มี 18 คำสั่ง:

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

---

## 17. CPU ทำงานจริง — ไล่ทีละ Clock

โปรแกรมตัวอย่าง: `LI $05 → ADDI $03 → SUBI $08`

```
ROM:
$0000: $30  (LI)
$0001: $05  (ค่า 5)
$0002: $10  (ADDI)
$0003: $03  (ค่า 3)
$0004: $90  (SUBI)
$0005: $08  (ค่า 8)
```

ไล่ทีละ clock:

```
Clock  Phase  PC    AC   Z   เกิดอะไร
-----  -----  ----  ---  --  ---------
1      T0     0000  ??   ?   อ่าน $30 → IR จำว่า "LI"
2      T1     0001  ??   ?   อ่าน $05 → IR จำว่า "5"
3      T2     0002  05   0   ทำ! AC = 5

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

7      T0     0004  08   0   อ่าน $90 → IR จำว่า "SUBI"
8      T1     0005  08   0   อ่าน $08 → IR จำว่า "8"
9      T2     0006  00   1   ทำ! AC = 8 - 8 = 0, Z=1!
```

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

---

## 18. อ่านจบแล้ว ทำอะไรต่อ?

| ขั้นถัดไป | เอกสาร |
|---|---|
| ต่อวงจรจริง (ทีละโมดูล) | `06_debug_plan.md` |
| ดูสายต่อทุกขา | `02_wiring_guide.md` |
| เขียนโปรแกรมให้ CPU | `tools/rv8gr_asm.py` |
| ดูตัวอย่างโปรแกรม .asm | `programs/` |
| เทียบ trace กับ simulator | `03_instruction_trace.md` |

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

---

## ตารางสรุปชิปทั้ง 34 ตัว

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

---

## ก่อนอื่น... ต้องรู้อะไรบ้าง?

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

ถ้ายังไม่เข้าใจตรงไหน ถามพี่ได้เลย! 🙂

---

## ภาคพิเศษ: ทำไมเลือกชิปตัวนี้? ทำไมต่อแบบนี้?

### ทำไมใช้ 74HC164 เป็น ring counter?

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

### ทำไม PC ใช้ 74HC161 × 4?

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

### ทำไมใช้ 74HC574 เป็น IR และ AC?

**ทางเลือกอื่น**: 74HC374, 74HC273
**ที่เลือก**: 74HC574 เพราะ:
- Edge-triggered (latch ที่ rising edge ของ CLK)
- มี /OE (ปิด output ได้) — ใช้กับ U14 และ U34 ตอนขับ IBUS
- Pinout เหมาะ: D1-D8 อยู่ด้านหนึ่ง, Q1-Q8 อยู่อีกด้าน → ต่อง่าย

### ทำไม XOR ทำหน้าที่ 3 อย่าง?

**ปัญหา**: ต้องการ ADD, SUB, XOR ใน ALU — ปกติต้องใช้ 3 วงจรแยก
**เคล็ดลับ**:
```
XOR(A, 0) = A        → ส่งค่าผ่านตรง (ใช้กับ ADD)
XOR(A, 1) = NOT(A)   → กลับบิต (ใช้กับ SUB)
XOR(A, B) = A^B      → คำนวณ XOR (ใช้กับ XOR instruction)
```
ใช้ mux (U19-U20) เลือก B-input → ชิป XOR ทำได้ทั้ง 3 หน้าที่!
ประหยัดชิปไป 4-6 ตัว เทียบกับ design ที่แยก logic unit ออก.

### ทำไม AC mux เลือกระหว่าง Adder กับ XOR output?

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

### ทำไม A15 ใช้เป็น chip select?

**ปัญหา**: ต้องแยก ROM กับ RAM → ปกติใช้ address decoder (74HC138)
**เคล็ดลับ**: ถ้าแบ่ง memory เป็น 2 ส่วนเท่าๆ กัน:
- Lower half ($0000+) = ROM → ใช้ A15 ตรงๆ
- Upper half ($8000+) = RAM → ใช้ NOT(A15)
- ไม่ต้องมี decoder! ใช้แค่ inverter 1 gate (U24)

### ทำไม Data Access ใช้ Data Page Register?

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

```
Data address = {Data Page (8 bit), Operand (8 bit)} = 16 bit = 64KB!
```

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

### ทำไม Z flag ใช้ async preset?

**ปัญหา**: ต้องรู้ว่า AC=0 หรือไม่ ก่อน BEQ/BNE ตัดสินใจ
**ทางเลือก**: synchronous (ใช้ D input + clock)
**ที่เลือก**: async preset เพราะ:
- U22 (688) ให้ /P=Q ที่ต่อ /PR ของ U21 ได้ตรงๆ
- ไม่ต้องมี inverter เพิ่ม (688 output = active-low = /PR input)
- ลด gate count 1 ตัว
- Z settle ทันใน 200ns (2 clock cycles ก่อนถูก sample)

### ทำไม BNE ใช้ SUB bit?

**ปัญหา**: BEQ ($02) jump เมื่อ Z=1, BNE ($82) jump เมื่อ Z=0
**เคล็ดลับ**: ใช้ XOR gate!
```
Z_match = Z_flag XOR SUB_bit
BEQ: SUB=0 → Z_match = Z (jump เมื่อ Z=1)
BNE: SUB=1 → Z_match = NOT(Z) (jump เมื่อ Z=0)
```
ไม่ต้องมี BR_TYPE bit แยก — reuse SUB bit ที่มีอยู่แล้ว!
ประหยัดบิตใน control byte (ใช้แค่ 8 บิต ครอบคลุม 18 คำสั่ง)

### ทำไมต้องปิด ROM ตอน STORE?

**ปัญหา**: Opcode = Control Word → ทุก combination ของ 8 บิตทำงานได้
**อันตราย**: ถ้า STORE ไป page ROM, U7 อาจขับ DBUS พร้อมกับ ROM
**วิธีแก้**: `ROM /OE = WR_DIR`
- ถ้า STR=1 → U7 เขียน IBUS→DBUS และ ROM output ถูกปิด
- 0 ชิปเพิ่ม (ใช้ gate ที่ว่างอยู่)

### ทำไมใช้ 2 bus (DBUS + IBUS)?

**ปัญหา**: ROM/RAM อยู่นอก CPU, ALU อยู่ใน CPU
**ถ้าใช้ bus เดียว**: ต้อง tristate ทุกชิปที่ต่อ bus → ซับซ้อน, มี contention risk สูง
**2 bus + bridge (U7)**:
- DBUS: เชื่อม ROM, RAM เท่านั้น (3 ตัว)
- IBUS: เชื่อม IR, ALU, AC, PG (ภายใน)
- U7 เป็นตัวกลาง — ควบคุมทิศ + enable/disable ได้

### สรุป: ปรัชญาการออกแบบ

| หลักการ | ตัวอย่าง |
|---|---|
| **Reuse** | XOR ทำ 3 หน้าที่ |
| **Direct control** | Opcode bit → hardware (no decoder) |
| **Minimal decode** | A15 = chip select (no 74HC138) |
| **Gate sharing** | SUB bit ใช้กับ BNE condition |
| **Bus isolation** | 2 buses + bridge ป้องกัน conflict |
| **Spare gates** | U25 gate 3, U28 gate D → ใช้ทำ guard |

ทุกการตัดสินใจมุ่งไปที่: **ใช้ชิปน้อยที่สุด แต่ยังทำงานถูกต้อง**
