JOJOCAFE/RV8/Programmer/KICAD/RV8Programmer.kicad_sch

## KiCad design Programmer/KICAD/RV8Programmer.kicad_sch (2026-06-21)

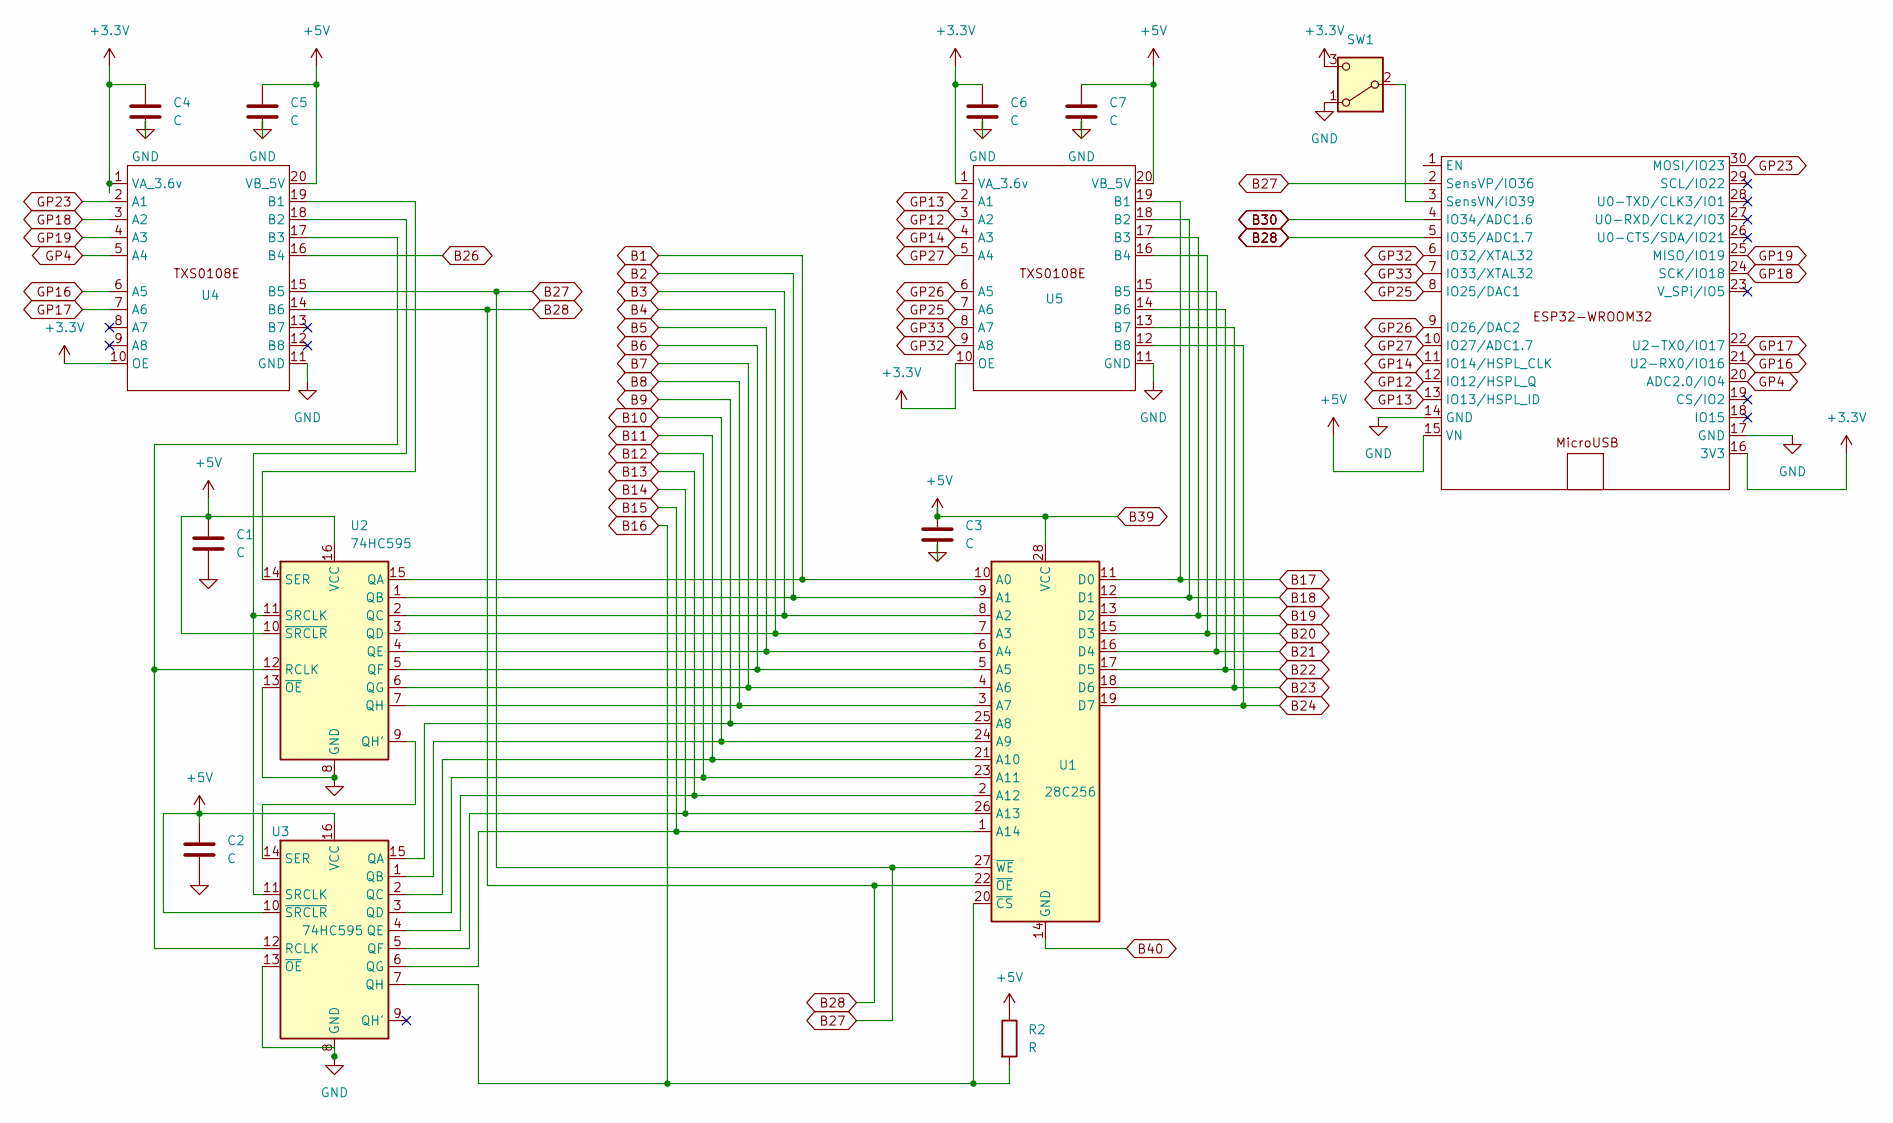
[picture p11: schematic RV8Programmer.kicad_sch]

Parts:
C1, C2, C3, C4, C5, C6, C7: C
R2: R
SW1: SW1
U1: 28C256
U2, U3: 74HC595
U4: TXS0108E
U5: TXS0108e5

Connections:
+3.3V: C4.1, C6.1, SW1.3 (C), U4.1 (VA_3.6v), U4.10 (OE), U5.1 (VA_3.6v), U5.10 (OE)
+5V: C1.1, C2.1, C3.1, C5.1, C7.1, R2.1, U1.28 (VCC), U2.10 (~SRCLR), U2.16 (VCC), U3.10 (~SRCLR), U3.16 (VCC), U4.20 (VB_5V), U5.20 (VB_5V)
B1: U1.10 (A0), U2.15 (QA)
B2: U1.9 (A1), U2.1 (QB)
B3: U1.8 (A2), U2.2 (QC)
B4: U1.7 (A3), U2.3 (QD)
B5: U1.6 (A4), U2.4 (QE)
B6: U1.5 (A5), U2.5 (QF)
B7: U1.4 (A6), U2.6 (QG)
B8: U1.3 (A7), U2.7 (QH)
B9: U1.25 (A8), U3.15 (QA)
B10: U1.24 (A9), U3.1 (QB)
B11: U1.21 (A10), U3.2 (QC)
B12: U1.23 (A11), U3.3 (QD)
B13: U1.2 (A12), U3.4 (QE)
B14: U1.26 (A13), U3.5 (QF)
B15: U1.1 (A14), U3.6 (QG)
B16: R2.2, U1.20 (~CS), U3.7 (QH)
B17: U1.11 (D0), U5.19 (B1)
B18: U1.12 (D1), U5.18 (B2)
B19: U1.13 (D2), U5.17 (B3)
B20: U1.15 (D3), U5.16 (B4)
B21: U1.16 (D4), U5.15 (B5)
B22: U1.17 (D5), U5.14 (B6)
B23: U1.18 (D6), U5.13 (B7)
B24: U1.19 (D7), U5.12 (B8)
B26: U4.16 (B4)
B27: U1.27 (~WE), U4.15 (B5)
B28: U1.22 (~OE), U4.14 (B6)
B40: U1.14 (GND)
GND: C1.2, C2.2, C3.2, C4.2, C5.2, C6.2, C7.2, SW1.1 (A), U2.8 (GND), U2.13 (~OE), U3.8 (GND), U3.13 (~OE), U4.11 (GND), U5.11 (GND)
GP4: U4.5 (A4)
GP12: U5.3 (A2)
GP13: U5.2 (A1)
GP14: U5.4 (A3)
GP16: U4.6 (A5)
GP17: U4.7 (A6)
GP18: U4.3 (A2)
GP19: U4.4 (A3)
GP23: U4.2 (A1)
GP25: U5.7 (A6)
GP26: U5.6 (A5)
GP27: U5.5 (A4)
GP32: U5.9 (A8)
GP33: U5.8 (A7)
unnamed: U2.9 (QH'), U3.14 (SER)
unnamed: U2.11 (SRCLK), U3.11 (SRCLK), U4.18 (B2)
unnamed: U2.12 (RCLK), U3.12 (RCLK), U4.17 (B3)
unnamed: U2.14 (SER), U4.19 (B1)
