JOJOCAFE/RV8/RV8GR/Kicad/ADDR_MEM.kicad_sch

## KiCad design RV8GR/Kicad/ADDR_MEM.kicad_sch (2026-07-09)

Schematic: ADDR_MEM.kicad_sch

Parts:
C15, C16, C17, C18: 100nF; C_Disc_D3.0mm_W1.6mm_P2.50mm
C_RAM: 100nF; C_Disc_D3.0mm_W1.6mm_P2.50mm
C_ROM: 100nF; C_Disc_D3.0mm_W1.6mm_P2.50mm
RAM1: 62256; DIP-28_W15.24mm
ROM1: AT28C256; DIP-28_W15.24mm
U15, U16, U29, U30: 74HC157; DIP-16_W7.62mm
