JOJOCAFE/RV8/RV8GR/Kicad/ALU_AC.kicad_sch

## KiCad design RV8GR/Kicad/ALU_AC.kicad_sch (2026-07-09)

Schematic: ALU_AC.kicad_sch

Parts:
C9, C10, C11, C12, C13, C17, C18, C19, C20, C21, C22: 100nF; C_Disc_D3.0mm_W1.6mm_P2.50mm
U9: 74HC574; DIP-20_W7.62mm
U10, U11: 74HC283; DIP-16_W7.62mm
U12, U13: 74HC86; DIP-14_W7.62mm
U17, U18, U19, U20: 74HC157; DIP-16_W7.62mm
U21: 74HC74; DIP-14_W7.62mm
U22: 74HC688; DIP-20_W7.62mm
