JOJOCAFE/RV8/RV8GR/Kicad/CLK_RST.kicad_sch

## KiCad design RV8GR/Kicad/CLK_RST.kicad_sch (2026-07-09)

Schematic: CLK_RST.kicad_sch

Parts:
C8: 100nF; C_Disc_D3.0mm_W1.6mm_P2.50mm
C_OSC: 100nF; C_Disc_D3.0mm_W1.6mm_P2.50mm
U8: 74HC164; DIP-14_W7.62mm
Y1: 1MHz; Oscillator_Module-4Pin
