JOJOCAFE/RV8/RV8GR/Kicad/CTRL.kicad_sch

## KiCad design RV8GR/Kicad/CTRL.kicad_sch (2026-07-09)

Schematic: CTRL.kicad_sch

Parts:
C23, C24, C25, C26, C27, C28, C31, C32, C33: 100nF; C_Disc_D3.0mm_W1.6mm_P2.50mm
U23, U32: 74HC574; DIP-20_W7.62mm
U24: 74HC04; DIP-14_W7.62mm
U25: 74HC32; DIP-14_W7.62mm
U26, U27: 74HC00; DIP-14_W7.62mm
U28: 74HC86; DIP-14_W7.62mm
U31: 74HC74; DIP-14_W7.62mm
U33: 74HC21; DIP-14_W7.62mm
