JOJOCAFE/RV8/RV8GR/Kicad/IR_BUF.kicad_sch

## KiCad design RV8GR/Kicad/IR_BUF.kicad_sch (2026-07-09)

Schematic: IR_BUF.kicad_sch

Parts:
C5, C6, C7, C14: 100nF; C_Disc_D3.0mm_W1.6mm_P2.50mm
U5, U6: 74HC574; DIP-20_W7.62mm
U7: 74HC245; DIP-20_W7.62mm
U14: 74HC541; DIP-20_W7.62mm
