JOJOCAFE/RV8/RV8GR/Kicad/PC.kicad_sch

## KiCad design RV8GR/Kicad/PC.kicad_sch (2026-07-09)

Schematic: PC.kicad_sch

Parts:
C1, C2, C3, C4: 100nF; C_Disc_D3.0mm_W1.6mm_P2.50mm
U1, U2, U3, U4: 74HC161; DIP-16_W7.62mm
