JOJOCAFE/RV8/RV8GR/rtl/rv8gr_chip_level.v

`timescale 1ns/1ps

module rv8gr_chip_level();
  wire n_bar_A15;
  wire n_bar_AC_BUF;
  wire n_bar_AC_WR;
  wire n_bar_ADDR_MODE;
  wire n_bar_BR_TAKEN;
  wire n_bar_IRL_OE;
  wire n_bar_IRQ;
  wire n_bar_JUMP;
  wire n_bar_PC_LD;
  wire n_bar_PG_cond;
  wire n_bar_P_EQ_Q;
  wire n_bar_RST;
  wire n_bar_T2;
  wire n_bar_XOR_MODE;
  wire n_ABUS0;
  wire n_ABUS1;
  wire n_ABUS10;
  wire n_ABUS11;
  wire n_ABUS12;
  wire n_ABUS13;
  wire n_ABUS14;
  wire n_ABUS15;
  wire n_ABUS2;
  wire n_ABUS3;
  wire n_ABUS4;
  wire n_ABUS5;
  wire n_ABUS6;
  wire n_ABUS7;
  wire n_ABUS8;
  wire n_ABUS9;
  wire n_AC0;
  wire n_AC1;
  wire n_AC2;
  wire n_AC3;
  wire n_AC4;
  wire n_AC5;
  wire n_AC6;
  wire n_AC7;
  wire n_ACC_CLK;
  wire n_AC_IN0;
  wire n_AC_IN1;
  wire n_AC_IN2;
  wire n_AC_IN3;
  wire n_AC_IN4;
  wire n_AC_IN5;
  wire n_AC_IN6;
  wire n_AC_IN7;
  wire n_AC_WR;
  wire n_ADDER_CARRY;
  wire n_ADDR_REQ;
  wire n_ALU_SUB;
  wire n_BR;
  wire n_BUF_OE_N;
  wire n_CLK;
  wire n_DBUS0;
  wire n_DBUS1;
  wire n_DBUS2;
  wire n_DBUS3;
  wire n_DBUS4;
  wire n_DBUS5;
  wire n_DBUS6;
  wire n_DBUS7;
  wire n_DP0;
  wire n_DP1;
  wire n_DP2;
  wire n_DP3;
  wire n_DP4;
  wire n_DP5;
  wire n_DP6;
  wire n_DP7;
  wire n_DP_Load;
  wire n_EI_decode;
  wire n_IBUS0;
  wire n_IBUS1;
  wire n_IBUS2;
  wire n_IBUS3;
  wire n_IBUS4;
  wire n_IBUS5;
  wire n_IBUS6;
  wire n_IBUS7;
  wire n_IE;
  wire n_IRL0;
  wire n_IRL1;
  wire n_IRL2;
  wire n_IRL3;
  wire n_IRL4;
  wire n_IRL5;
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
  assign n_U5_10 = 1'b0;
  assign n_U5_20 = 1'b1;
  assign n_U6_1 = 1'b0;
  assign n_U6_10 = 1'b0;
  assign n_U6_20 = 1'b1;
  assign n_U7_10 = 1'b0;
  assign n_U7_20 = 1'b1;
  assign n_U8_14 = 1'b1;
  assign n_U8_7 = 1'b0;
  assign n_U9_1 = 1'b0;
  assign n_U9_10 = 1'b0;
  assign n_U9_20 = 1'b1;

  mem_62256 RAM1 (.A({n_ABUS14, n_ABUS13, n_ABUS12, n_ABUS11, n_ABUS10, n_ABUS9, n_ABUS8, n_ABUS7, n_ABUS6, n_ABUS5, n_ABUS4, n_ABUS3, n_ABUS2, n_ABUS1, n_ABUS0}), .DQ({n_DBUS7, n_DBUS6, n_DBUS5, n_DBUS4, n_DBUS3, n_DBUS2, n_DBUS1, n_DBUS0}), .CE_bar(n_bar_A15), .OE_bar(n_RAM1_22), .WE_bar(n_bar_AC_BUF));
  mem_at28c256 ROM1 (.A({n_ABUS14, n_ABUS13, n_ABUS12, n_ABUS11, n_ABUS10, n_ABUS9, n_ABUS8, n_ABUS7, n_ABUS6, n_ABUS5, n_ABUS4, n_ABUS3, n_ABUS2, n_ABUS1, n_ABUS0}), .DQ({n_DBUS7, n_DBUS6, n_DBUS5, n_DBUS4, n_DBUS3, n_DBUS2, n_DBUS1, n_DBUS0}), .CE_bar(n_ABUS15), .OE_bar(n_WR_DIR), .WE_bar(1'b1));
  ttl_74hc161 #(.DELAY_RISE(1), .DELAY_FALL(1)) U1 (.Clear_bar(n_bar_RST), .Load_bar(n_bar_PC_LD), .ENT(n_PC_INC), .ENP(n_PC_INC), .D({n_IRL3, n_IRL2, n_IRL1, n_IRL0}), .Clk(n_CLK), .RCO(n_RCO_0), .Q({n_PC3, n_PC2, n_PC1, n_PC0}));
  ttl_74hc283 #(.DELAY_RISE(1), .DELAY_FALL(1)) U10 (.A({n_AC3, n_AC2, n_AC1, n_AC0}), .B({n_XOR_Y3, n_XOR_Y2, n_XOR_Y1, n_XOR_Y0}), .C_in(n_ALU_SUB), .Sum({n_SUM3, n_SUM2, n_SUM1, n_SUM0}), .C_out(n_ADDER_CARRY));
  ttl_74hc283 #(.DELAY_RISE(1), .DELAY_FALL(1)) U11 (.A({n_AC7, n_AC6, n_AC5, n_AC4}), .B({n_XOR_Y7, n_XOR_Y6, n_XOR_Y5, n_XOR_Y4}), .C_in(n_ADDER_CARRY), .Sum({n_SUM7, n_SUM6, n_SUM5, n_SUM4}), .C_out(open_U11_9));
  ttl_74hc86 #(.DELAY_RISE(1), .DELAY_FALL(1)) U12 (.A({n_IBUS3, n_IBUS2, n_IBUS1, n_IBUS0}), .B({n_XOR_B3, n_XOR_B2, n_XOR_B1, n_XOR_B0}), .Y({n_XOR_Y3, n_XOR_Y2, n_XOR_Y1, n_XOR_Y0}));
  ttl_74hc86 #(.DELAY_RISE(1), .DELAY_FALL(1)) U13 (.A({n_IBUS7, n_IBUS6, n_IBUS5, n_IBUS4}), .B({n_XOR_B7, n_XOR_B6, n_XOR_B5, n_XOR_B4}), .Y({n_XOR_Y7, n_XOR_Y6, n_XOR_Y5, n_XOR_Y4}));
  ttl_74hc541 #(.DELAY_RISE(1), .DELAY_FALL(1)) U14 (.OE1_bar(n_bar_AC_BUF), .OE2_bar(n_bar_AC_BUF), .A({n_AC7, n_AC6, n_AC5, n_AC4, n_AC3, n_AC2, n_AC1, n_AC0}), .Y({n_IBUS7, n_IBUS6, n_IBUS5, n_IBUS4, n_IBUS3, n_IBUS2, n_IBUS1, n_IBUS0}));
  ttl_74hc157 #(.DELAY_RISE(1), .DELAY_FALL(1)) U15 (.Enable_bar(n_U15_15), .Select(n_bar_ADDR_MODE), .A({n_IRL3, n_IRL2, n_IRL1, n_IRL0}), .B({n_PC3, n_PC2, n_PC1, n_PC0}), .Y({n_ABUS3, n_ABUS2, n_ABUS1, n_ABUS0}));
  ttl_74hc157 #(.DELAY_RISE(1), .DELAY_FALL(1)) U16 (.Enable_bar(n_U16_15), .Select(n_bar_ADDR_MODE), .A({n_IRL7, n_IRL6, n_IRL5, n_IRL4}), .B({n_PC7, n_PC6, n_PC5, n_PC4}), .Y({n_ABUS7, n_ABUS6, n_ABUS5, n_ABUS4}));
  ttl_74hc157 #(.DELAY_RISE(1), .DELAY_FALL(1)) U17 (.Enable_bar(n_U17_15), .Select(n_MUX_SEL), .A({n_SUM3, n_SUM2, n_SUM1, n_SUM0}), .B({n_XOR_Y3, n_XOR_Y2, n_XOR_Y1, n_XOR_Y0}), .Y({n_AC_IN3, n_AC_IN2, n_AC_IN1, n_AC_IN0}));
  ttl_74hc157 #(.DELAY_RISE(1), .DELAY_FALL(1)) U18 (.Enable_bar(n_U18_15), .Select(n_MUX_SEL), .A({n_SUM7, n_SUM6, n_SUM5, n_SUM4}), .B({n_XOR_Y7, n_XOR_Y6, n_XOR_Y5, n_XOR_Y4}), .Y({n_AC_IN7, n_AC_IN6, n_AC_IN5, n_AC_IN4}));
  ttl_74hc157 #(.DELAY_RISE(1), .DELAY_FALL(1)) U19 (.Enable_bar(n_U19_15), .Select(n_XOR_MODE), .A({n_ALU_SUB, n_ALU_SUB, n_ALU_SUB, n_ALU_SUB}), .B({n_AC3, n_AC2, n_AC1, n_AC0}), .Y({n_XOR_B3, n_XOR_B2, n_XOR_B1, n_XOR_B0}));
  ttl_74hc161 #(.DELAY_RISE(1), .DELAY_FALL(1)) U2 (.Clear_bar(n_bar_RST), .Load_bar(n_bar_PC_LD), .ENT(n_RCO_0), .ENP(n_PC_INC), .D({n_IRL7, n_IRL6, n_IRL5, n_IRL4}), .Clk(n_CLK), .RCO(n_RCO_1), .Q({n_PC7, n_PC6, n_PC5, n_PC4}));
  ttl_74hc157 #(.DELAY_RISE(1), .DELAY_FALL(1)) U20 (.Enable_bar(n_U20_15), .Select(n_XOR_MODE), .A({n_ALU_SUB, n_ALU_SUB, n_ALU_SUB, n_ALU_SUB}), .B({n_AC7, n_AC6, n_AC5, n_AC4}), .Y({n_XOR_B7, n_XOR_B6, n_XOR_B5, n_XOR_B4}));
  ttl_74hc74 #(.DELAY_RISE(1), .DELAY_FALL(1), .SAMPLE_DELAY(20)) U21 (.Preset_bar({n_U21_10, n_bar_P_EQ_Q}), .Clear_bar({n_U21_13, n_U21_1}), .D({n_U21_12, n_U21_2}), .Clk({n_U21_11, n_ACC_CLK}), .Q({open_U21_9, n_Z_flag}), .Q_bar({open_U21_8, open_U21_6}));
  ttl_74hc688 #(.DELAY_RISE(1), .DELAY_FALL(1)) U22 (.Enable_bar(n_U22_1), .A({n_AC7, n_AC6, n_AC5, n_AC4, n_AC3, n_AC2, n_AC1, n_AC0}), .B({n_U22_18, n_U22_16, n_U22_14, n_U22_12, n_U22_9, n_U22_7, n_U22_5, n_U22_3}), .Equal_bar(n_bar_P_EQ_Q));
  ttl_74hc574 #(.DELAY_RISE(1), .DELAY_FALL(1)) U23 (.OE_bar(n_U23_1), .Clk(n_PG_CLK), .D({n_IBUS7, n_IBUS6, n_IBUS5, n_IBUS4, n_IBUS3, n_IBUS2, n_IBUS1, n_IBUS0}), .Q({n_PG7, n_PG6, n_PG5, n_PG4, n_PG3, n_PG2, n_PG1, n_PG0}));
  ttl_74hc04 #(.DELAY_RISE(1), .DELAY_FALL(1)) U24 (.A({n_bar_IRL_OE, n_AC_WR, n_JMP, n_ABUS15, n_T1, n_T0}), .Y({n_BUF_OE_N, n_bar_AC_WR, n_bar_JUMP, n_bar_A15, n_NOT_T1, n_NOT_T0}));
  ttl_74hc32 #(.DELAY_RISE(1), .DELAY_FALL(1)) U25 (.A({n_bar_T2, n_U25_9, n_T0, n_SRC}), .B({n_bar_PG_cond, n_U25_10, n_T1, n_STR}), .Y({n_PG_CLK, open_U25_8, n_PC_INC, n_ADDR_REQ}));
  ttl_74hc00 #(.DELAY_RISE(8), .DELAY_FALL(8)) U26 (.A({n_T2, n_T2, n_ADDR_REQ, n_T2}), .B({n_PC_LOAD_COND, n_STR, n_T2, n_bar_ADDR_MODE}), .Y({n_bar_PC_LD, n_bar_AC_BUF, n_bar_ADDR_MODE, n_bar_IRL_OE}));
  ttl_74hc00 #(.DELAY_RISE(1), .DELAY_FALL(1)) U27 (.A({n_T2, n_MUX_SEL, n_bar_JUMP, n_BR}), .B({n_AC_WR, n_bar_AC_WR, n_bar_BR_TAKEN, n_Z_match}), .Y({n_ACC_CLK, n_bar_PG_cond, n_PC_LOAD_COND, n_bar_BR_TAKEN}));
  ttl_74hc86 #(.DELAY_RISE(1), .DELAY_FALL(1)) U28 (.A({n_XOR_MODE, n_bar_AC_BUF, n_T2, n_Z_flag}), .B({n_U28_13, n_U28_10, n_U28_5, n_ALU_SUB}), .Y({n_bar_XOR_MODE, n_WR_DIR, n_bar_T2, n_Z_match}));
  ttl_74hc157 #(.DELAY_RISE(1), .DELAY_FALL(1)) U29 (.Enable_bar(n_U29_15), .Select(n_bar_ADDR_MODE), .A({n_DP3, n_DP2, n_DP1, n_DP0}), .B({n_PC11, n_PC10, n_PC9, n_PC8}), .Y({n_ABUS11, n_ABUS10, n_ABUS9, n_ABUS8}));
  ttl_74hc161 #(.DELAY_RISE(1), .DELAY_FALL(1)) U3 (.Clear_bar(n_bar_RST), .Load_bar(n_bar_PC_LD), .ENT(n_RCO_1), .ENP(n_PC_INC), .D({n_PG3, n_PG2, n_PG1, n_PG0}), .Clk(n_CLK), .RCO(n_RCO_2), .Q({n_PC11, n_PC10, n_PC9, n_PC8}));
  ttl_74hc157 #(.DELAY_RISE(1), .DELAY_FALL(1)) U30 (.Enable_bar(n_U30_15), .Select(n_bar_ADDR_MODE), .A({n_DP7, n_DP6, n_DP5, n_DP4}), .B({n_PC15, n_PC14, n_PC13, n_PC12}), .Y({n_ABUS15, n_ABUS14, n_ABUS13, n_ABUS12}));
  ttl_74hc74 #(.DELAY_RISE(1), .DELAY_FALL(1)) U31 (.Preset_bar({n_U31_10, n_U31_4}), .Clear_bar({n_bar_RST, n_bar_RST}), .D({n_U31_12, n_U31_2}), .Clk({n_bar_IRQ, n_EI_decode}), .Q({n_IRQ_FF, n_IE}), .Q_bar({open_U31_8, open_U31_6}));
  ttl_74hc574 #(.DELAY_RISE(1), .DELAY_FALL(1), .SAMPLE_DELAY(40)) U32 (.OE_bar(n_U32_1), .Clk(n_DP_Load), .D({n_IBUS7, n_IBUS6, n_IBUS5, n_IBUS4, n_IBUS3, n_IBUS2, n_IBUS1, n_IBUS0}), .Q({n_DP7, n_DP6, n_DP5, n_DP4, n_DP3, n_DP2, n_DP1, n_DP0}));
  ttl_74hc21 #(.DELAY_RISE(15), .DELAY_FALL(15)) U33 (.A({n_T2, n_T2}), .B({n_SRC, n_XOR_MODE}), .C({n_bar_XOR_MODE, n_bar_ADDR_MODE}), .D({n_bar_AC_WR, n_bar_AC_WR}), .Y({n_EI_decode, n_DP_Load}));
  ttl_74hc541 #(.DELAY_RISE(1), .DELAY_FALL(1)) U34 (.OE1_bar(n_bar_IRL_OE), .OE2_bar(n_bar_IRL_OE), .A({n_IRL7, n_IRL6, n_IRL5, n_IRL4, n_IRL3, n_IRL2, n_IRL1, n_IRL0}), .Y({n_IBUS7, n_IBUS6, n_IBUS5, n_IBUS4, n_IBUS3, n_IBUS2, n_IBUS1, n_IBUS0}));
  ttl_74hc161 #(.DELAY_RISE(1), .DELAY_FALL(1)) U4 (.Clear_bar(n_bar_RST), .Load_bar(n_bar_PC_LD), .ENT(n_RCO_2), .ENP(n_PC_INC), .D({n_PG7, n_PG6, n_PG5, n_PG4}), .Clk(n_CLK), .RCO(open_U4_15), .Q({n_PC15, n_PC14, n_PC13, n_PC12}));
  ttl_74hc574 #(.DELAY_RISE(1), .DELAY_FALL(1), .SAMPLE_DELAY(40)) U5 (.OE_bar(n_U5_1), .Clk(n_T0), .D({n_IBUS7, n_IBUS6, n_IBUS5, n_IBUS4, n_IBUS3, n_IBUS2, n_IBUS1, n_IBUS0}), .Q({n_ALU_SUB, n_XOR_MODE, n_MUX_SEL, n_AC_WR, n_SRC, n_STR, n_BR, n_JMP}));
  ttl_74hc574 #(.DELAY_RISE(1), .DELAY_FALL(1), .SAMPLE_DELAY(40)) U6 (.OE_bar(n_U6_1), .Clk(n_T1), .D({n_IBUS7, n_IBUS6, n_IBUS5, n_IBUS4, n_IBUS3, n_IBUS2, n_IBUS1, n_IBUS0}), .Q({n_IRL7, n_IRL6, n_IRL5, n_IRL4, n_IRL3, n_IRL2, n_IRL1, n_IRL0}));
  ttl_74hc245 #(.DELAY_RISE(1), .DELAY_FALL(1)) U7 (.OE_bar(n_BUF_OE_N), .DIR(n_WR_DIR), .A({n_IBUS7, n_IBUS6, n_IBUS5, n_IBUS4, n_IBUS3, n_IBUS2, n_IBUS1, n_IBUS0}), .B({n_DBUS7, n_DBUS6, n_DBUS5, n_DBUS4, n_DBUS3, n_DBUS2, n_DBUS1, n_DBUS0}));
  ttl_74hc164 #(.DELAY_RISE(4), .DELAY_FALL(4)) U8 (.Clear_bar(n_bar_RST), .Clk(n_CLK), .A(n_NOT_T0), .B(n_NOT_T1), .Q({open_U8_13, open_U8_12, open_U8_11, open_U8_10, open_U8_6, n_T2, n_T1, n_T0}));
  ttl_74hc574 #(.DELAY_RISE(1), .DELAY_FALL(1)) U9 (.OE_bar(n_U9_1), .Clk(n_ACC_CLK), .D({n_AC_IN7, n_AC_IN6, n_AC_IN5, n_AC_IN4, n_AC_IN3, n_AC_IN2, n_AC_IN1, n_AC_IN0}), .Q({n_AC7, n_AC6, n_AC5, n_AC4, n_AC3, n_AC2, n_AC1, n_AC0}));
endmodule
