JOJOCAFE/RV8/RV8GR/tb/tb_rv8gr_setdp.v

// RV8-GR Testbench — SETDP large RAM test (5KB + ROM read)
// Memory map: ROM $0000-$7FFF, RAM $8000-$FFFF
// Default data_page = $80 (registers at $80xx in RAM)
`timescale 1ns/1ps

module tb_rv8gr_setdp;
    reg clk, rst_n;
    wire halted;

    rv8gr_cpu cpu(.clk(clk), .rst_n(rst_n), .irq_n(1'b1), .halted(halted));

    always #5 clk = ~clk;
    integer cycle_count;
    reg [1023:0] dumpfile;

    initial begin
        if (!$value$plusargs("dumpfile=%s", dumpfile))
            dumpfile = "rv8gr_setdp.vcd";
        $dumpfile(dumpfile);
        $dumpvars(0, tb_rv8gr_setdp);

        // Write phase: SETDP to RAM pages $90/$95/$A0/$A3
        cpu.rom[0]  = 8'h40; cpu.rom[1]  = 8'h90; // SETDP $90
        cpu.rom[2]  = 8'h30; cpu.rom[3]  = 8'h90; // LI $90
        cpu.rom[4]  = 8'h04; cpu.rom[5]  = 8'h00; // SB $00 → RAM[$9000]
        cpu.rom[6]  = 8'h04; cpu.rom[7]  = 8'h80; // SB $80 → RAM[$9080]
        cpu.rom[8]  = 8'h04; cpu.rom[9]  = 8'hFF; // SB $FF → RAM[$90FF]
        cpu.rom[10] = 8'h40; cpu.rom[11] = 8'h95; // SETDP $95
        cpu.rom[12] = 8'h30; cpu.rom[13] = 8'h95; // LI $95
        cpu.rom[14] = 8'h04; cpu.rom[15] = 8'h00; // SB $00 → RAM[$9500]
        cpu.rom[16] = 8'h04; cpu.rom[17] = 8'h40; // SB $40 → RAM[$9540]
        cpu.rom[18] = 8'h40; cpu.rom[19] = 8'hA0; // SETDP $A0
        cpu.rom[20] = 8'h30; cpu.rom[21] = 8'hA0; // LI $A0
        cpu.rom[22] = 8'h04; cpu.rom[23] = 8'h00; // SB $00 → RAM[$A000]
        cpu.rom[24] = 8'h04; cpu.rom[25] = 8'hFF; // SB $FF → RAM[$A0FF]
        cpu.rom[26] = 8'h40; cpu.rom[27] = 8'hA3; // SETDP $A3
        cpu.rom[28] = 8'h30; cpu.rom[29] = 8'hA3; // LI $A3
        cpu.rom[30] = 8'h04; cpu.rom[31] = 8'hFF; // SB $FF → RAM[$A3FF]
        // Read phase
        cpu.rom[32] = 8'h40; cpu.rom[33] = 8'h90; // SETDP $90
        cpu.rom[34] = 8'h38; cpu.rom[35] = 8'h00; // LB $00
        cpu.rom[36] = 8'h90; cpu.rom[37] = 8'h90; // SUBI $90
        cpu.rom[38] = 8'h02; cpu.rom[39] = 8'h2A; // BEQ $2A
        cpu.rom[40] = 8'h01; cpu.rom[41] = 8'h7C; // J fail
        cpu.rom[42] = 8'h38; cpu.rom[43] = 8'hFF; // LB $FF
        cpu.rom[44] = 8'h90; cpu.rom[45] = 8'h90; // SUBI $90
        cpu.rom[46] = 8'h02; cpu.rom[47] = 8'h32; // BEQ $32
        cpu.rom[48] = 8'h01; cpu.rom[49] = 8'h7C; // J fail
        cpu.rom[50] = 8'h40; cpu.rom[51] = 8'h95; // SETDP $95
        cpu.rom[52] = 8'h38; cpu.rom[53] = 8'h00; // LB $00
        cpu.rom[54] = 8'h90; cpu.rom[55] = 8'h95; // SUBI $95
        cpu.rom[56] = 8'h02; cpu.rom[57] = 8'h3C; // BEQ $3C
        cpu.rom[58] = 8'h01; cpu.rom[59] = 8'h7C; // J fail
        cpu.rom[60] = 8'h38; cpu.rom[61] = 8'h40; // LB $40
        cpu.rom[62] = 8'h90; cpu.rom[63] = 8'h95; // SUBI $95
        cpu.rom[64] = 8'h02; cpu.rom[65] = 8'h44; // BEQ $44
        cpu.rom[66] = 8'h01; cpu.rom[67] = 8'h7C; // J fail
        cpu.rom[68] = 8'h40; cpu.rom[69] = 8'hA0; // SETDP $A0
        cpu.rom[70] = 8'h38; cpu.rom[71] = 8'h00; // LB $00
        cpu.rom[72] = 8'h90; cpu.rom[73] = 8'hA0; // SUBI $A0
        cpu.rom[74] = 8'h02; cpu.rom[75] = 8'h4E; // BEQ $4E
        cpu.rom[76] = 8'h01; cpu.rom[77] = 8'h7C; // J fail
        cpu.rom[78] = 8'h38; cpu.rom[79] = 8'hFF; // LB $FF
        cpu.rom[80] = 8'h90; cpu.rom[81] = 8'hA0; // SUBI $A0
        cpu.rom[82] = 8'h02; cpu.rom[83] = 8'h56; // BEQ $56
        cpu.rom[84] = 8'h01; cpu.rom[85] = 8'h7C; // J fail
        cpu.rom[86] = 8'h40; cpu.rom[87] = 8'hA3; // SETDP $A3
        cpu.rom[88] = 8'h38; cpu.rom[89] = 8'hFF; // LB $FF
        cpu.rom[90] = 8'h90; cpu.rom[91] = 8'hA3; // SUBI $A3
        cpu.rom[92] = 8'h02; cpu.rom[93] = 8'h60; // BEQ $60
        cpu.rom[94] = 8'h01; cpu.rom[95] = 8'h7C; // J fail
        // ROM read test via SETDP $00
        cpu.rom[96] = 8'h40; cpu.rom[97] = 8'h00; // SETDP $00
        cpu.rom[98] = 8'h38; cpu.rom[99] = 8'h00; // LB $00 → ROM[$0000] = $40
        cpu.rom[100]= 8'h90; cpu.rom[101]= 8'h40; // SUBI $40
        cpu.rom[102]= 8'h02; cpu.rom[103]= 8'h6A; // BEQ $6A
        cpu.rom[104]= 8'h01; cpu.rom[105]= 8'h7C; // J fail
        // Default RAM page ($80) register test
        cpu.rom[106]= 8'h40; cpu.rom[107]= 8'h80; // SETDP $80
        cpu.rom[108]= 8'h30; cpu.rom[109]= 8'h77; // LI $77
        cpu.rom[110]= 8'h04; cpu.rom[111]= 8'h05; // SB $05 → RAM[$8005]
        cpu.rom[112]= 8'h30; cpu.rom[113]= 8'h00; // LI $00
        cpu.rom[114]= 8'h38; cpu.rom[115]= 8'h05; // LB $05 → RAM[$8005]
        cpu.rom[116]= 8'h90; cpu.rom[117]= 8'h77; // SUBI $77
        cpu.rom[118]= 8'h02; cpu.rom[119]= 8'h7A; // BEQ pass
        cpu.rom[120]= 8'h01; cpu.rom[121]= 8'h7C; // J fail
        // pass:
        cpu.rom[122]= 8'h01; cpu.rom[123]= 8'h7A; // HLT
        // fail:
        cpu.rom[124]= 8'h30; cpu.rom[125]= 8'hFF; // LI $FF
        cpu.rom[126]= 8'h01; cpu.rom[127]= 8'h7E; // HLT

        // Reset
        clk = 0; rst_n = 0;
        #20 rst_n = 1;

        // Run
        cycle_count = 0;
        while (!halted && cycle_count < 1000) begin
            @(posedge clk);
            cycle_count = cycle_count + 1;
        end

        if (!halted) begin
            $display("FAIL: Timeout after %0d cycles", cycle_count);
            $fatal(1, "SETDP test timed out");
        end else if (cpu.ac == 8'hFF) begin
            $display("FAIL: Test failed at cycle %0d, PC=$%04X", cycle_count, cpu.pc);
            $fatal(1, "SETDP test reached the fail halt");
        end
        else begin
            $display("=== SETDP TEST PASSED === (%0d cycles)", cycle_count);
            $display("  5KB RAM write/read across pages $90-$A3: OK");
            $display("  ROM read via SETDP $00: OK");
            $display("  Default RAM page ($80) registers: OK");
        end

        $finish;
    end
endmodule
